Farex-GH/Open-Genbu-GC/PCB/pico-pcb/pico-pcb.kicad_sch

## KiCad design PCB/pico-pcb/pico-pcb.kicad_sch (2022-03-07)

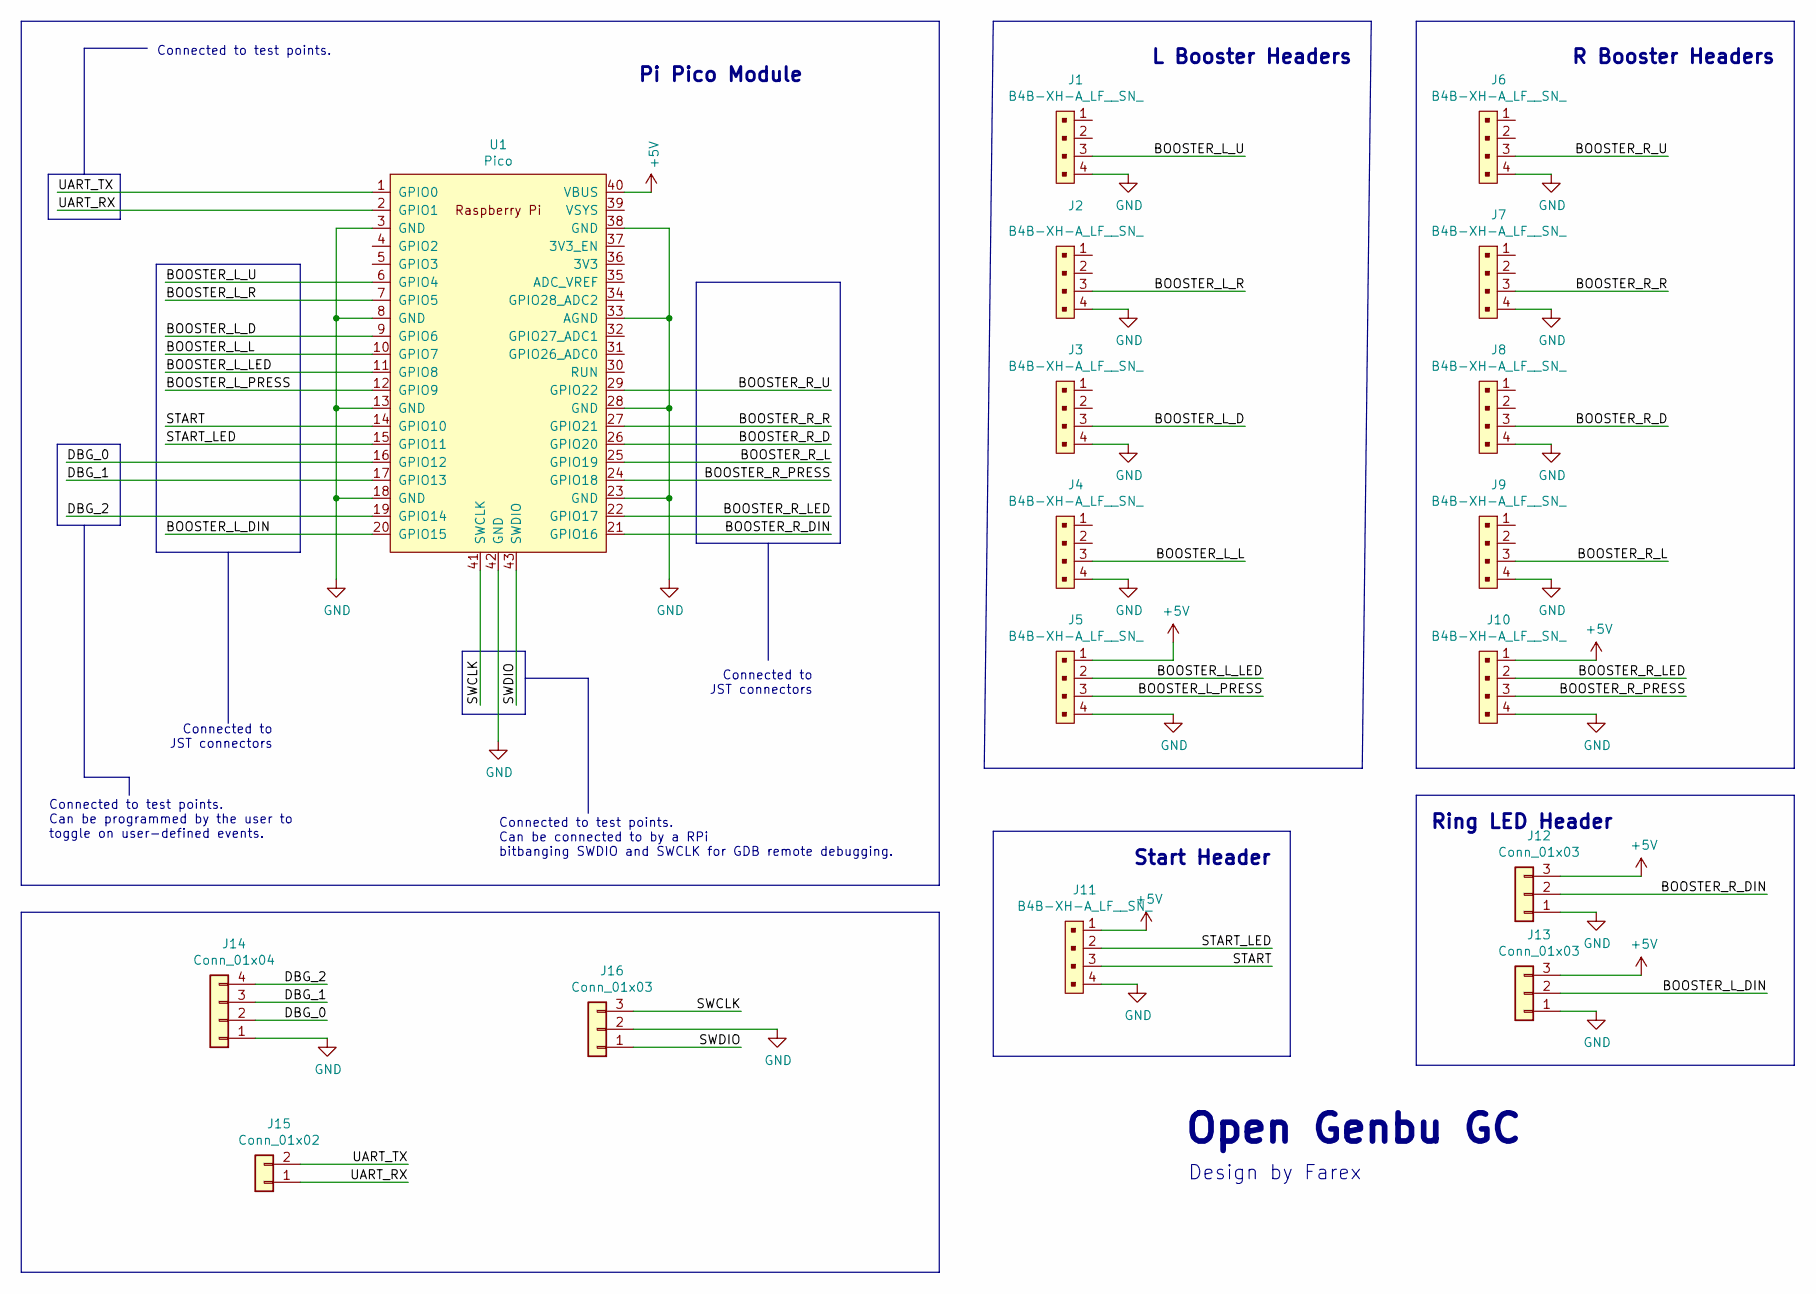
[picture p2: schematic pico-pcb.kicad_sch]

Parts:
J1, J2, J3, J4, J5, J6, J7, J8, J9, J10, J11: B4B-XH-A_LF__SN_; JST_B4B-XH-A(LF)(SN); MPN B4B-XH-A(LF)(SN); Digi-Key_PN 455-2249-ND
J12, J13, J16: Conn_01x03; PinSocket_1x03_P2.54mm_Vertical
J14: Conn_01x04; PinSocket_1x04_P2.54mm_Vertical
J15: Conn_01x02; PinSocket_1x02_P2.54mm_Vertical
U1: Pico; RPi_Pico_SMD_TH

Connections:
+5V: J5.1, J10.1, J11.1, J12.3, J13.3, U1.40 (VBUS)
BOOSTER_L_D: J3.3, U1.9 (GPIO6)
BOOSTER_L_DIN: J13.2, U1.20 (GPIO15)
BOOSTER_L_L: J4.3, U1.10 (GPIO7)
BOOSTER_L_LED: J5.2, U1.11 (GPIO8)
BOOSTER_L_PRESS: J5.3, U1.12 (GPIO9)
BOOSTER_L_R: J2.3, U1.7 (GPIO5)
BOOSTER_L_U: J1.3, U1.6 (GPIO4)
BOOSTER_R_D: J8.3, U1.26 (GPIO20)
BOOSTER_R_DIN: J12.2, U1.21 (GPIO16)
BOOSTER_R_L: J9.3, U1.25 (GPIO19)
BOOSTER_R_LED: J10.2, U1.22 (GPIO17)
BOOSTER_R_PRESS: J10.3, U1.24 (GPIO18)
BOOSTER_R_R: J7.3, U1.27 (GPIO21)
BOOSTER_R_U: J6.3, U1.29 (GPIO22)
DBG_0: J14.2, U1.16 (GPIO12)
DBG_1: J14.3, U1.17 (GPIO13)
DBG_2: J14.4, U1.19 (GPIO14)
GND: J1.4, J2.4, J3.4, J4.4, J5.4, J6.4, J7.4, J8.4, J9.4, J10.4, J11.4, J12.1, J13.1, J14.1, J16.2, U1.3 (GND), U1.8 (GND), U1.13 (GND), U1.18 (GND), U1.23 (GND), U1.28 (GND), U1.33 (AGND), U1.38 (GND), U1.42 (GND)
START: J11.3, U1.14 (GPIO10)
START_LED: J11.2, U1.15 (GPIO11)
SWCLK: J16.3, U1.41 (SWCLK)
SWDIO: J16.1, U1.43 (SWDIO)
UART_RX: J15.1, U1.2 (GPIO1)
UART_TX: J15.2, U1.1 (GPIO0)

Notes on the sheet:
Connected to test points. Can be programmed by the user to toggle on user-defined events.
Connected to test points.
Connected to JST connectors
Pi Pico Module
R Booster Headers
Connected to test points. Can be connected to by a RPi bitbanging SWDIO and SWCLK for GDB remote debugging.
L Booster Headers
Ring LED Header
Start Header
Open Genbu GC
Design by Farex
