Farex-GH/Open-Genbu-GC/PCB/front-panel/front-panel/front-panel.kicad_sch

## KiCad design PCB/front-panel/front-panel/front-panel.kicad_sch (2022-03-07)

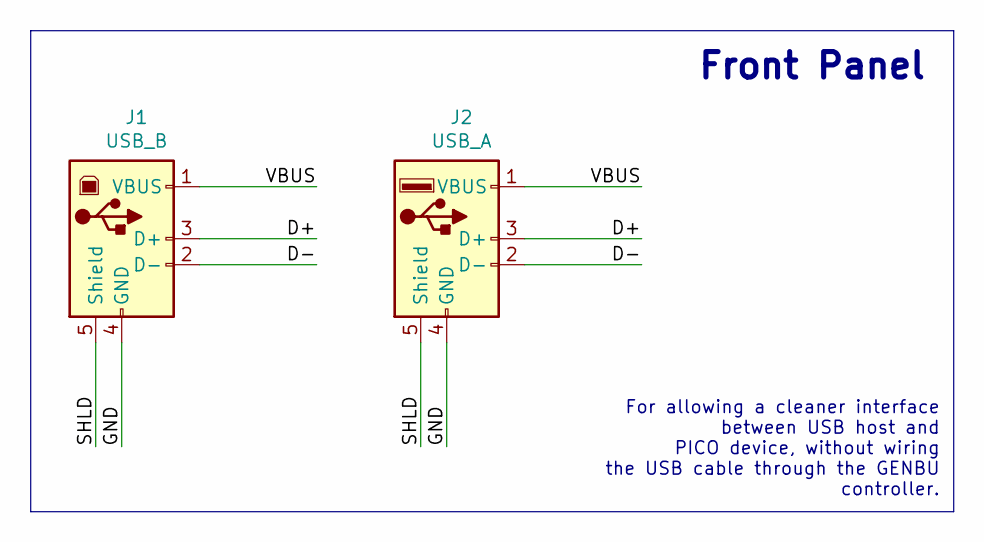
[picture p3: schematic front-panel.kicad_sch]

Parts:
J1: USB_B; USB_B_TE_5787834_Vertical
J2: USB_A; USB_A_Molex_105057_Vertical

Connections:
D+: J1.3 (D+), J2.3 (D+)
D-: J1.2 (D-), J2.2 (D-)
GND: J1.4 (GND), J2.4 (GND)
SHLD: J1.5 (Shield), J2.5 (Shield)
VBUS: J1.1 (VBUS), J2.1 (VBUS)

Notes on the sheet:
Front Panel
For allowing a cleaner interface between USB host and PICO device, without wiring the USB cable through the GENBU controller.
