Farex-GH/Open-Genbu-GC/firmware/debounce.h

#ifndef DEBOUNCE_H
#define DEBOUNCE_H

#include <stdint.h>
#include <stdbool.h>

#include "pico/stdlib.h"
#include "hardware/gpio.h"

#include "board_io.h"

#define DEBOUNCE_SLIDE_TIME_MS 15
/*
 * This shit bounces like crazy.
 * The microswitch is the same as slides, but the button has its own bounce.
 * This is bad enough where it may interfere with normal play.
 */
#define DEBOUNCE_PRESS_TIME_MS 50

#endif
